Gabapentin/Arduino-RC-6CH-Radio-control/Docs/Images/Arduino_Power_Supply_160.png

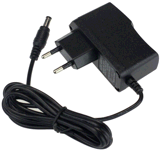
Docs/Images/Arduino_Power_Supply_160.png
