Gabapentin/Arduino-RC-6CH-Radio-control/Docs/Images/Buzzer_480.png

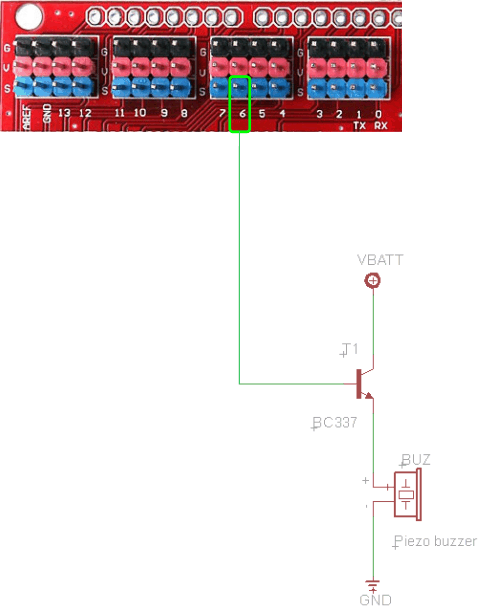
Docs/Images/Buzzer_480.png
