Gabapentin/Arduino-RC-6CH-Radio-control/Docs/Images/Gimbal_1_240.png

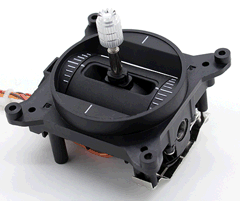
Docs/Images/Gimbal_1_240.png
