Gabapentin/Arduino-RC-6CH-Radio-control/Docs/Images/Gimbal_2_240.png

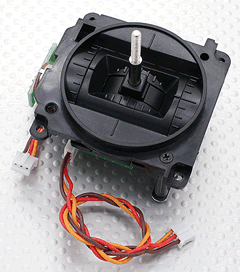
Docs/Images/Gimbal_2_240.png
