Gabapentin/Arduino-RC-6CH-Radio-control/Docs/Images/Key_buttons.png

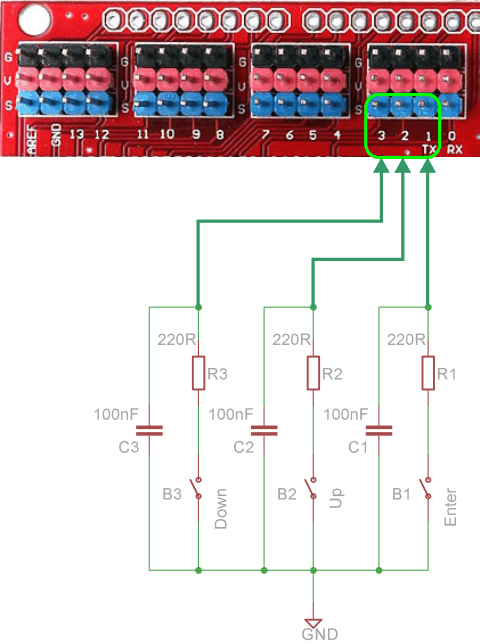
Docs/Images/Key_buttons.png
