Gabapentin/Arduino-RC-6CH-Radio-control/Docs/Images/Lion_240.png

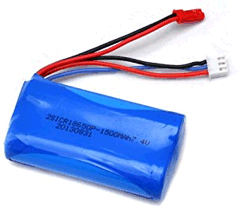
Docs/Images/Lion_240.png
