Gabapentin/Arduino-RC-6CH-Radio-control/Docs/Images/Lipo_240.png

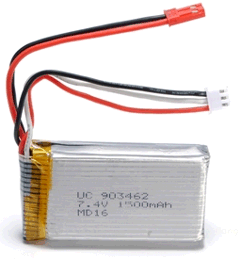
Docs/Images/Lipo_240.png
