Gabapentin/Arduino-RC-6CH-Radio-control/Docs/Images/LM317_Supply_160.png

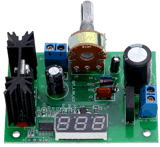
Docs/Images/LM317_Supply_160.png
