Gabapentin/Arduino-RC-6CH-Radio-control/Docs/Images/Nano_Shield_160.png

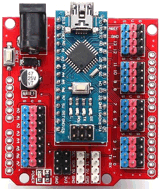
Docs/Images/Nano_Shield_160.png
