Gabapentin/Arduino-RC-6CH-Radio-control/Docs/Images/Nano_Shield_Blue_240.png

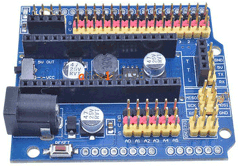
Docs/Images/Nano_Shield_Blue_240.png
