Gabapentin/Arduino-RC-6CH-Radio-control/Docs/Images/Oled_rear_240.png

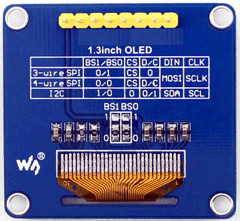
Docs/Images/Oled_rear_240.png
