Gabapentin/Arduino-RC-6CH-Radio-control/Docs/Images/Pot_160.png

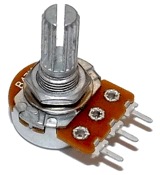
Docs/Images/Pot_160.png
