Gabapentin/Arduino-RC-6CH-Radio-control/Docs/Images/RC_pot_160.png

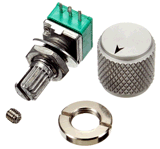
Docs/Images/RC_pot_160.png
