Gabapentin/Arduino-RC-6CH-Radio-control/Docs/Images/Slide_SW_160.png

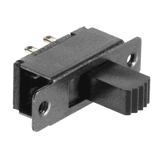
Docs/Images/Slide_SW_160.png
