Gabapentin/Arduino-RC-6CH-Radio-control/Docs/Images/Switch_long.png

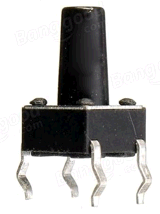
Docs/Images/Switch_long.png
