Gabapentin/Arduino-RC-6CH-Radio-control/Docs/Images/Switch_short.png

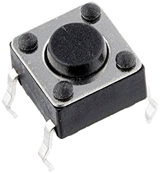
Docs/Images/Switch_short.png
