Gabapentin/Arduino-RC-6CH-Radio-control/Docs/Images/Gimbals_wiring_mode1_480.png

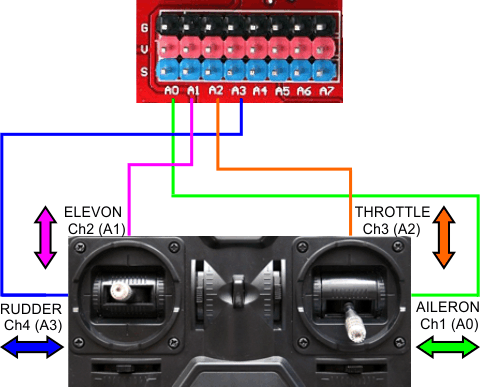
Docs/Images/Gimbals_wiring_mode1_480.png
