Gabapentin/Arduino-RC-6CH-Radio-control/Docs/Images/OLED_wiring.png

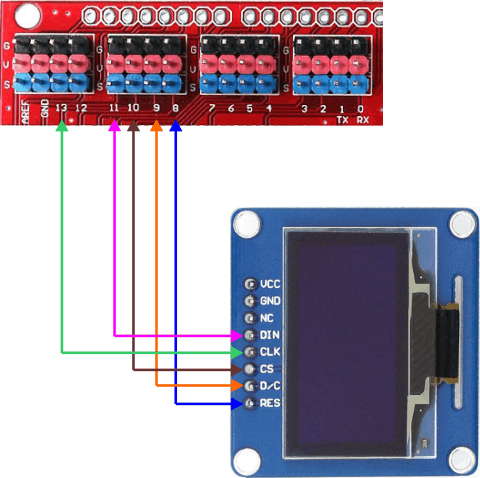
Docs/Images/OLED_wiring.png
