Gabapentin/Arduino-RC-6CH-Radio-control/Docs/Images/PPM_wiring.png

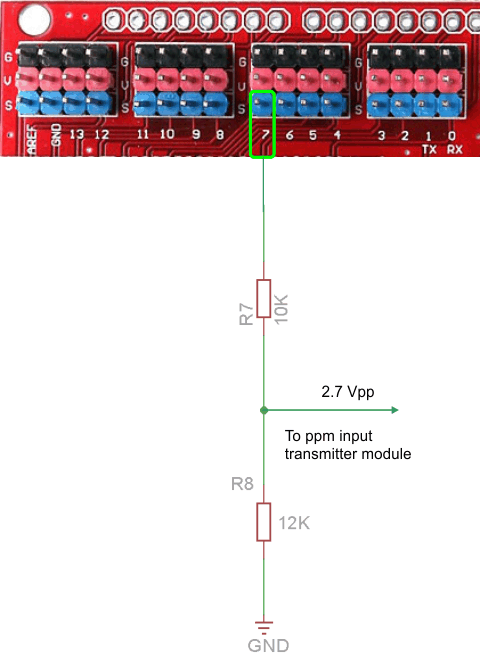
Docs/Images/PPM_wiring.png
