Gabapentin/Arduino-RC-6CH-Radio-control/Docs/Images/Switch_wiring_2_480.png

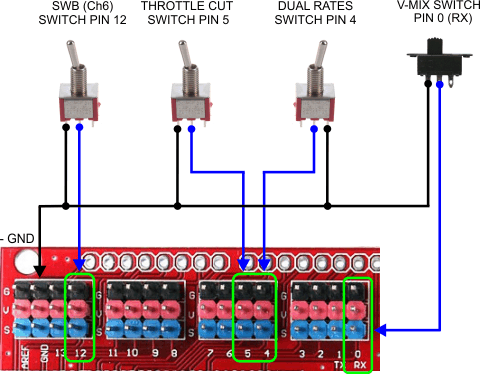
Docs/Images/Switch_wiring_2_480.png
